Charlie1qa/PerfecTea/cad/Back.PNG

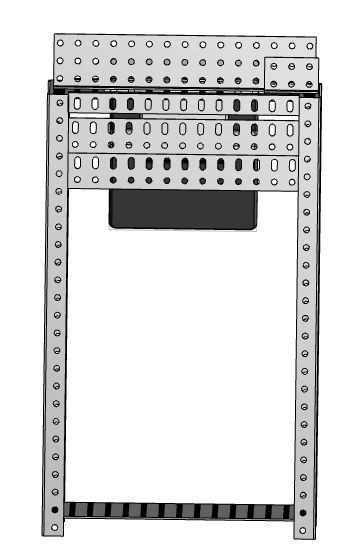
cad/Back.PNG
