Charlie1qa/PerfecTea/cad/Front.PNG

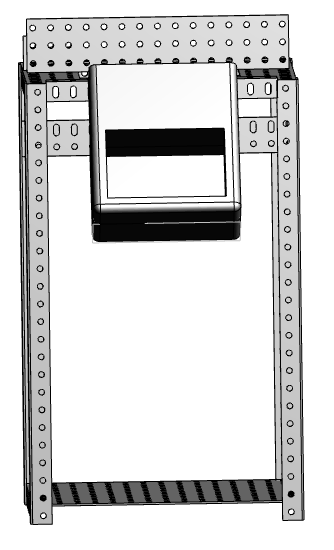
cad/Front.PNG
