Charlie1qa/PerfecTea/cad/Side.PNG

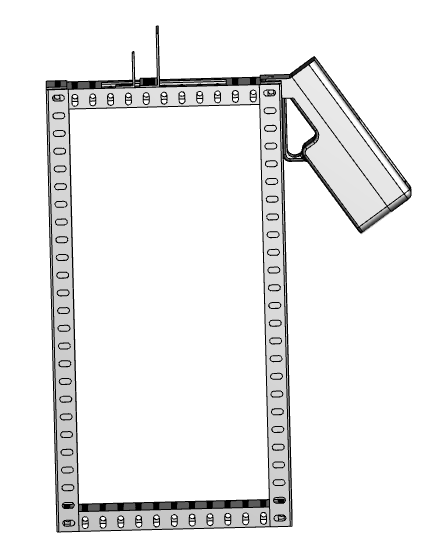
cad/Side.PNG
