Charlie1qa/PerfecTea/cad/Top.PNG

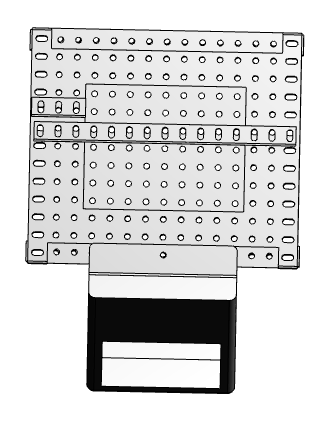
cad/Top.PNG
