Charlie1qa/PerfecTea/perfectea_gui/img/title1.png

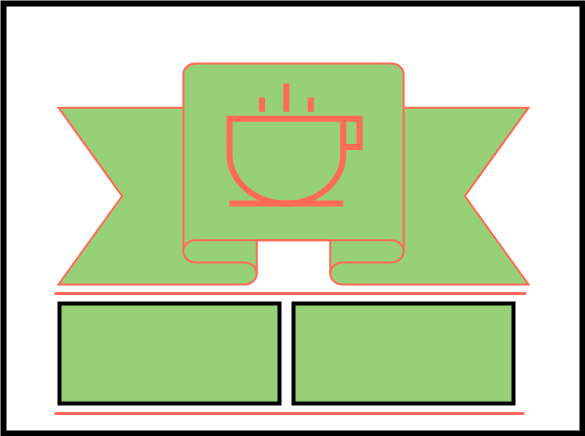
perfectea_gui/img/title1.png
